FLMRobert/OpenLedModule/Lamp25CMLED/Images/25CMLED__small.jpg

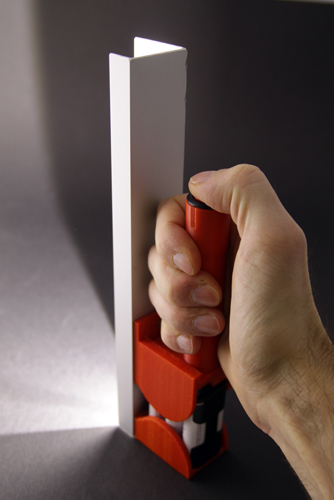
Lamp25CMLED/Images/25CMLED__small.jpg
