FLMRobert/OpenLedModule/Lamp25CMLED/Images/25CMLEDModule1Prototype.JPG

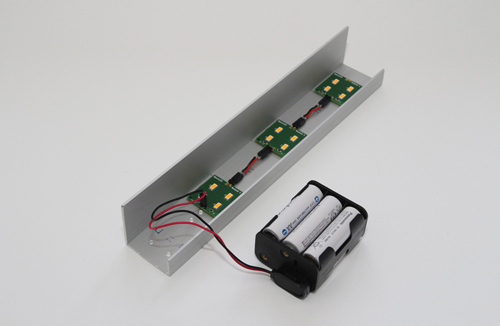
Lamp25CMLED/Images/25CMLEDModule1Prototype.JPG
