FLMRobert/OpenLedModule/Lamp40FLATLED/Images/40FLATLEDPrototype_small.jpg

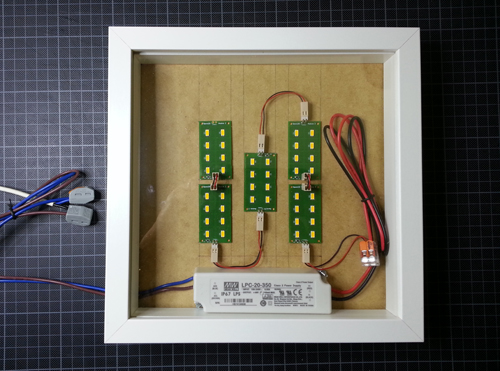
Lamp40FLATLED/Images/40FLATLEDPrototype_small.jpg
