FLMRobert/OpenLedModule/Module2/Images/LEDModul2Detail_02.png

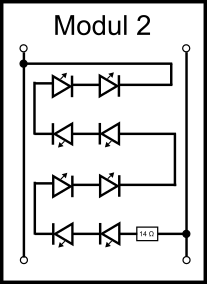
Module2/Images/LEDModul2Detail_02.png
