FLMRobert/OpenLedModule/Lamp25CMLED/Images/Assembly/01.jpg

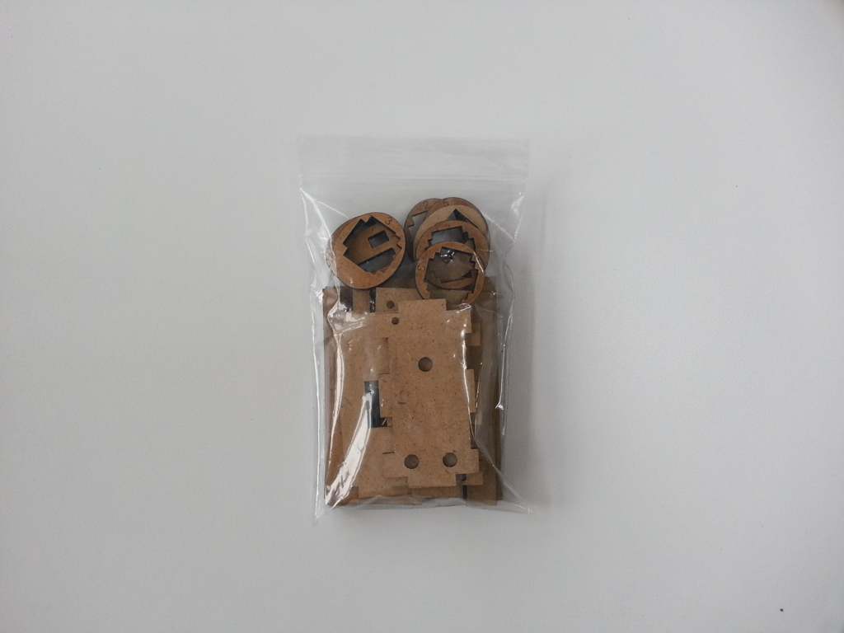
Lamp25CMLED/Images/Assembly/01.jpg
