FLMRobert/OpenLedModule/Lamp25CMLED/Images/Assembly/02.jpg

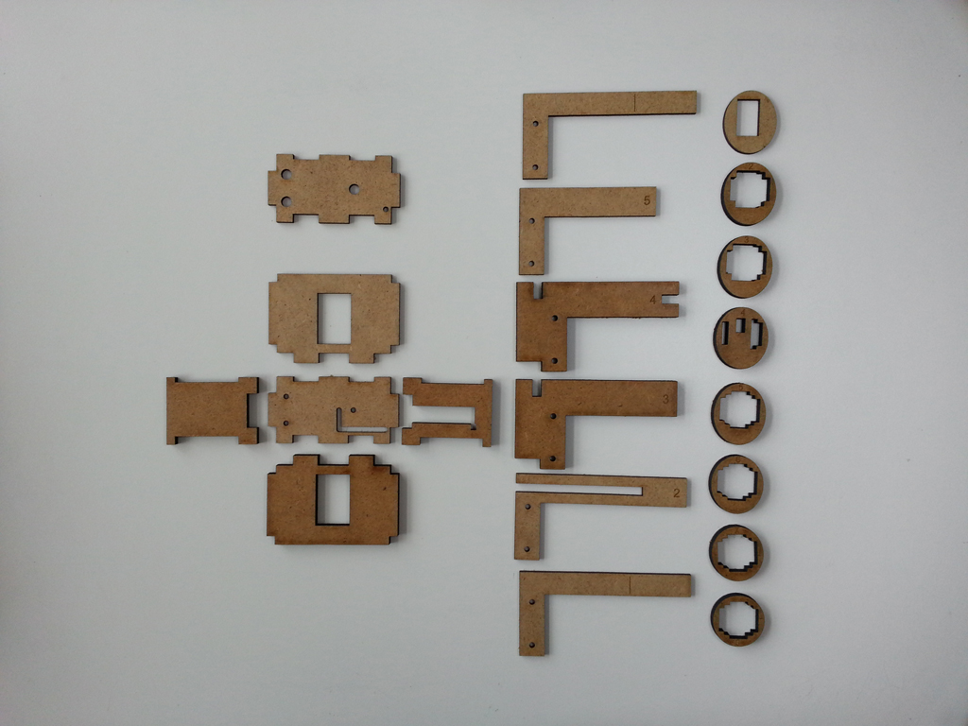
Lamp25CMLED/Images/Assembly/02.jpg
