FLMRobert/OpenLedModule/Lamp25CMLED/Images/Assembly/04.jpg

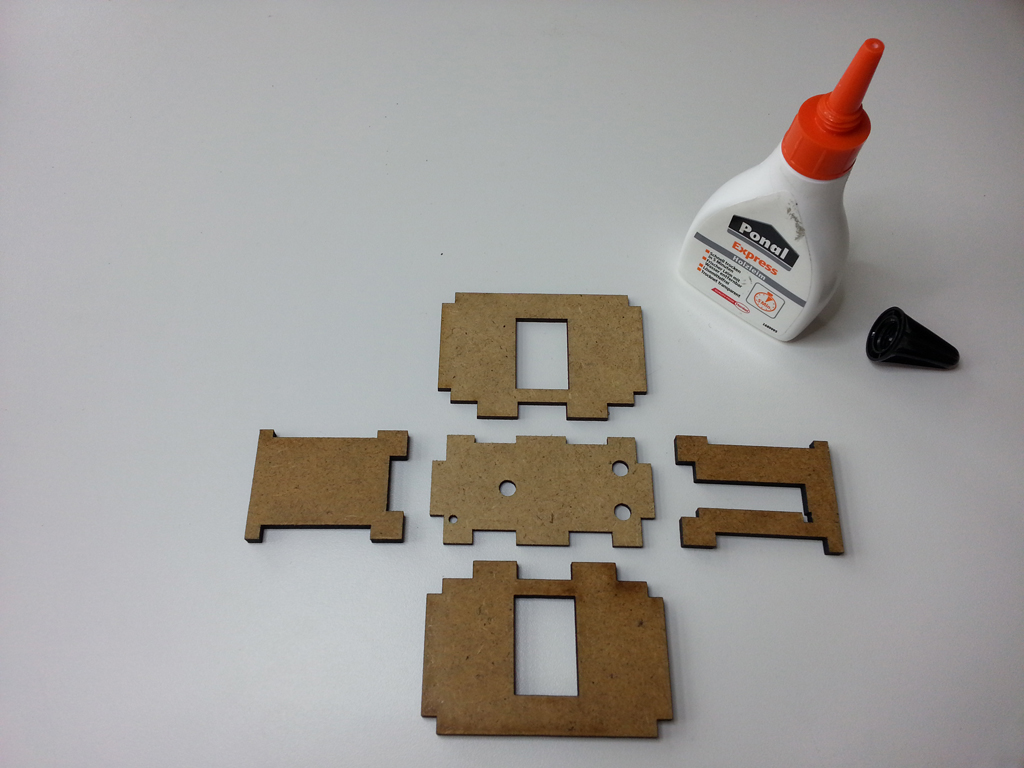
Lamp25CMLED/Images/Assembly/04.jpg
