FLMRobert/OpenLedModule/Lamp25CMLED/Images/Assembly/05.jpg

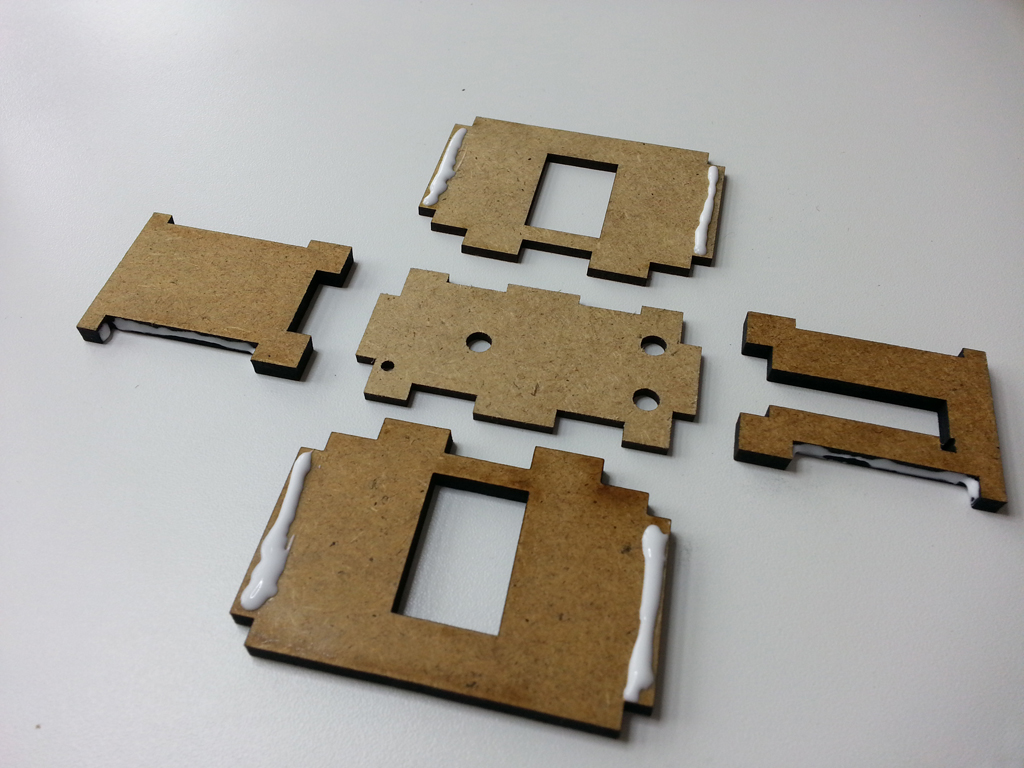
Lamp25CMLED/Images/Assembly/05.jpg
