FLMRobert/OpenLedModule/Lamp25CMLED/Images/Assembly/06.jpg

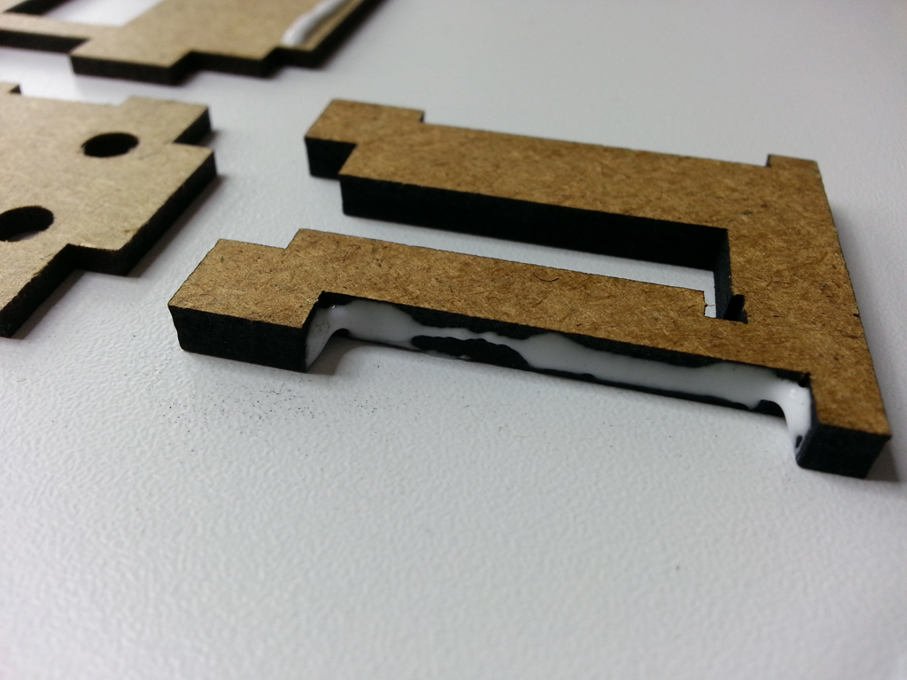
Lamp25CMLED/Images/Assembly/06.jpg
