FLMRobert/OpenLedModule/Lamp25CMLED/Images/Assembly/07.jpg

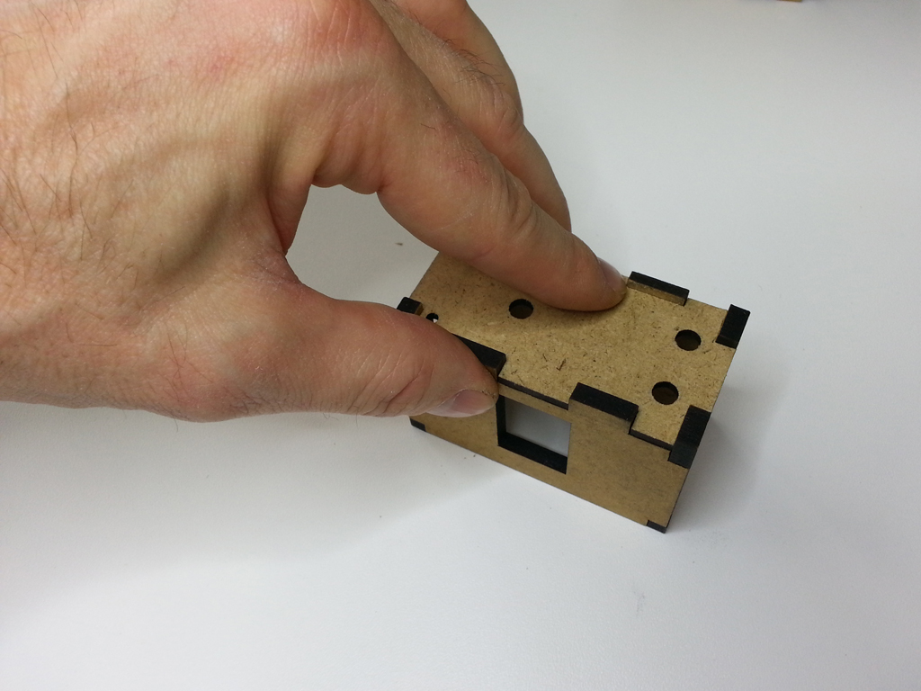
Lamp25CMLED/Images/Assembly/07.jpg
