FLMRobert/OpenLedModule/Lamp25CMLED/Images/Assembly/08.jpg

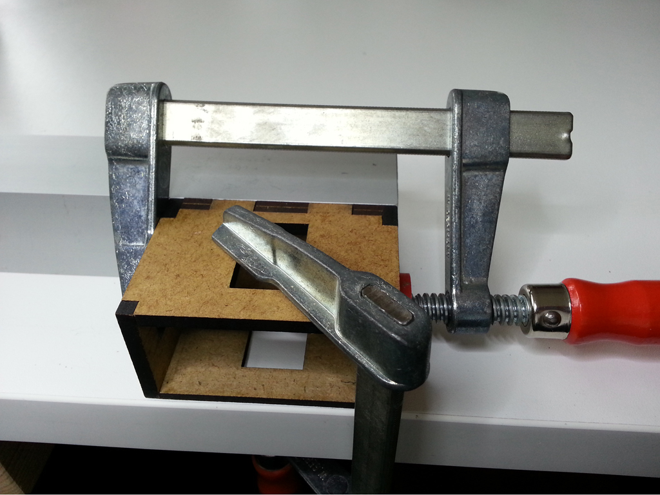
Lamp25CMLED/Images/Assembly/08.jpg
