FLMRobert/OpenLedModule/Lamp25CMLED/Images/Assembly/09.jpg

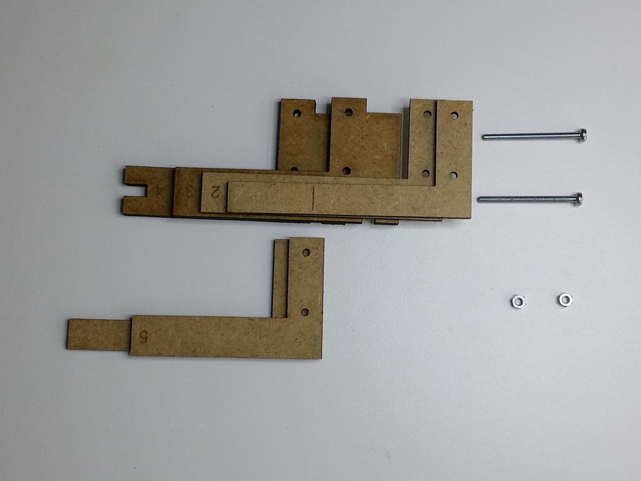
Lamp25CMLED/Images/Assembly/09.jpg
