FLMRobert/OpenLedModule/Lamp25CMLED/Images/Assembly/10.jpg

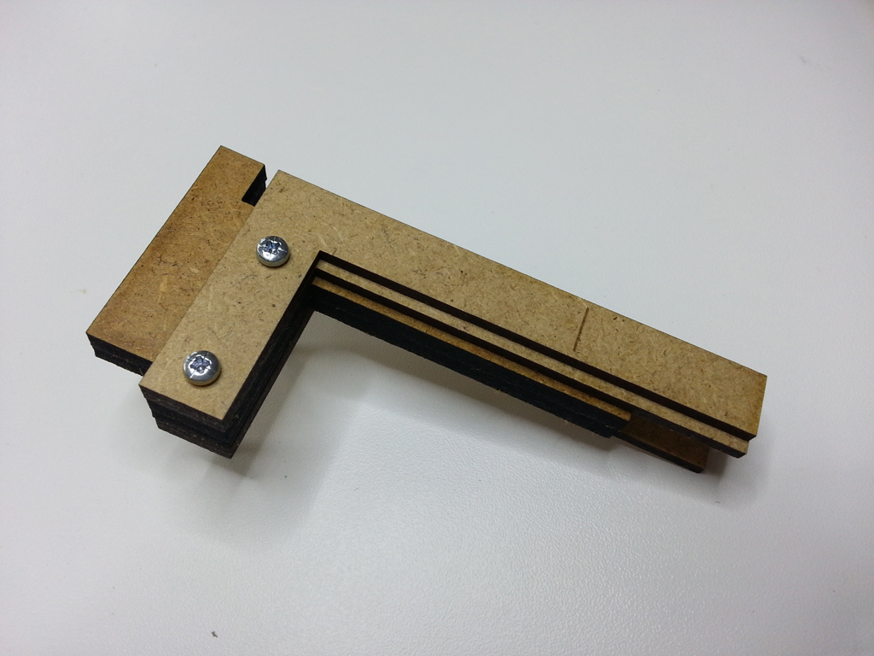
Lamp25CMLED/Images/Assembly/10.jpg
