FLMRobert/OpenLedModule/Lamp25CMLED/Images/Assembly/12.jpg

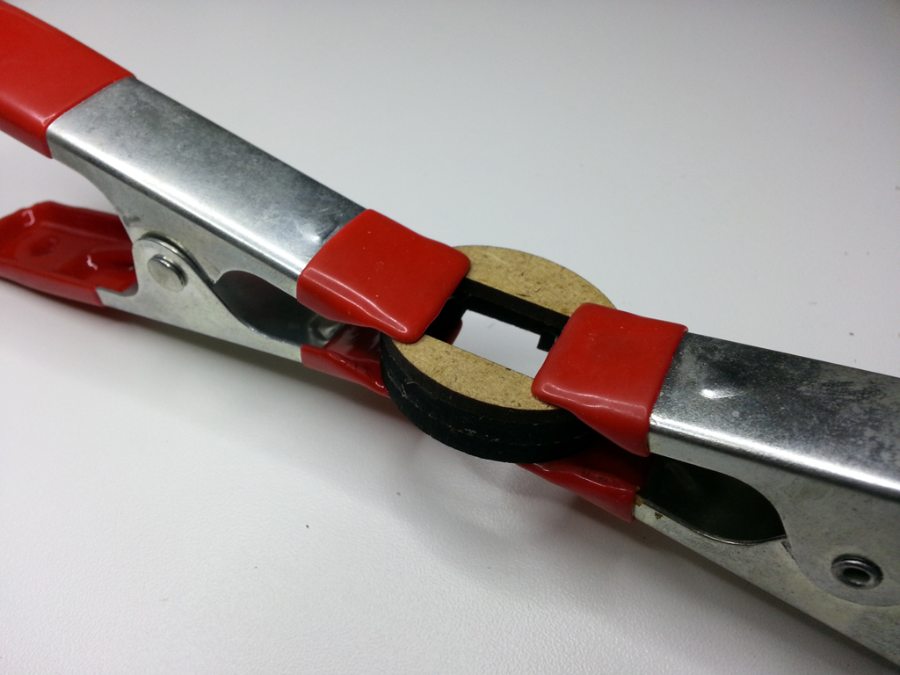
Lamp25CMLED/Images/Assembly/12.jpg
