FLMRobert/OpenLedModule/Lamp25CMLED/Images/Assembly/13.jpg

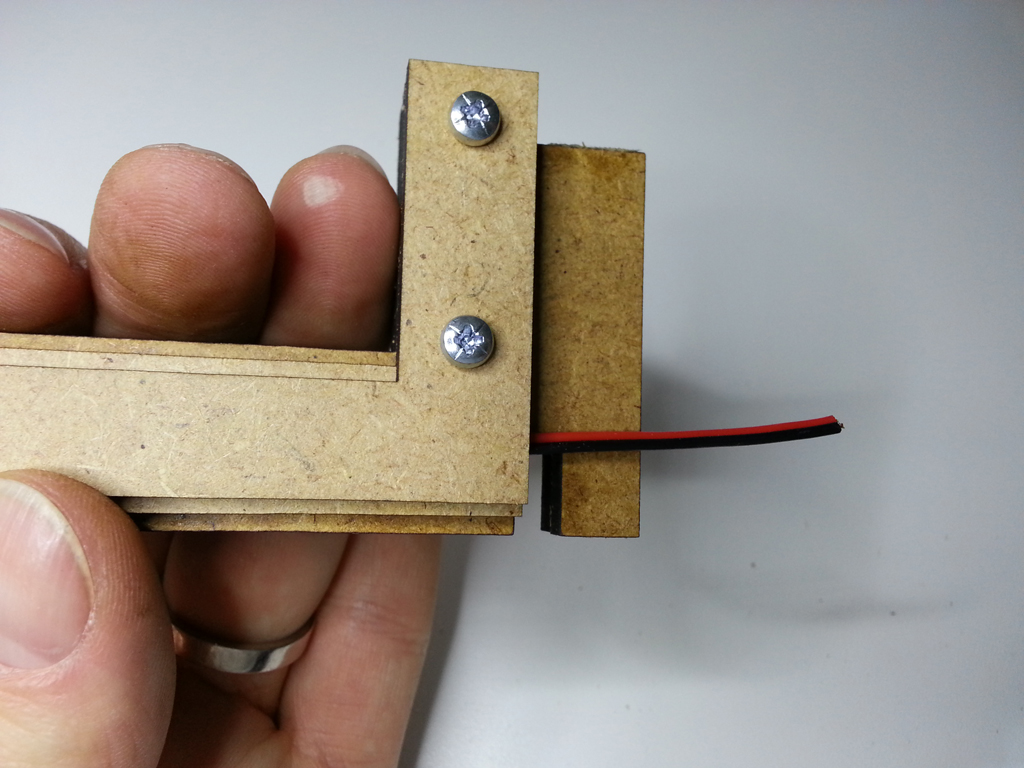
Lamp25CMLED/Images/Assembly/13.jpg
