FLMRobert/OpenLedModule/Lamp25CMLED/Images/Assembly/14.jpg

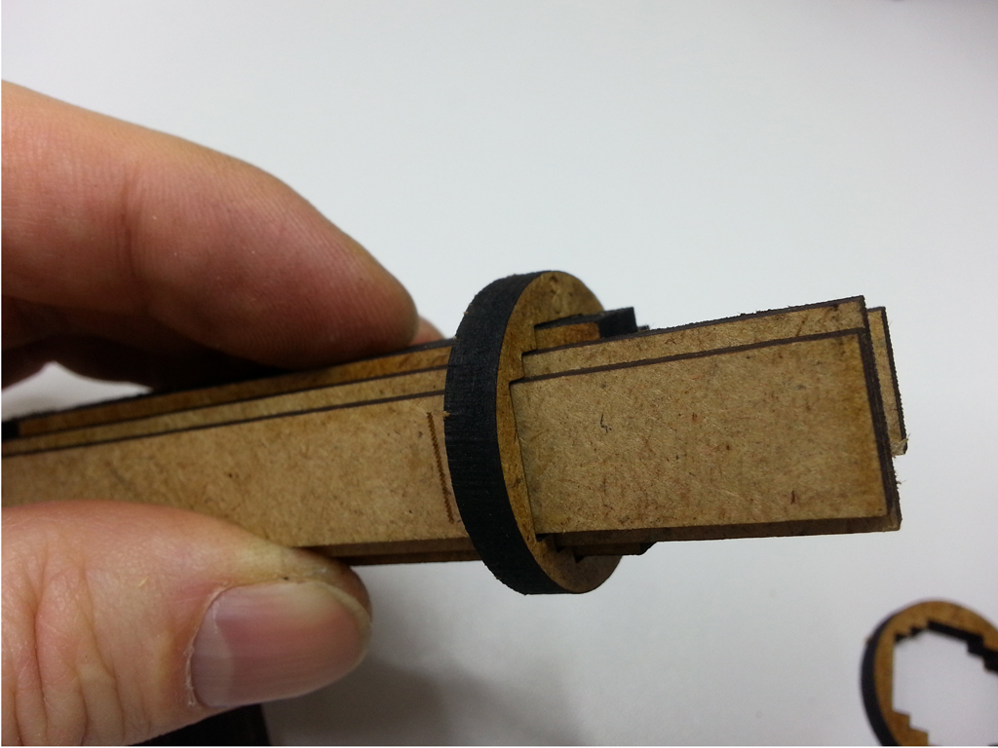
Lamp25CMLED/Images/Assembly/14.jpg
