FLMRobert/OpenLedModule/Lamp25CMLED/Images/Assembly/15.jpg

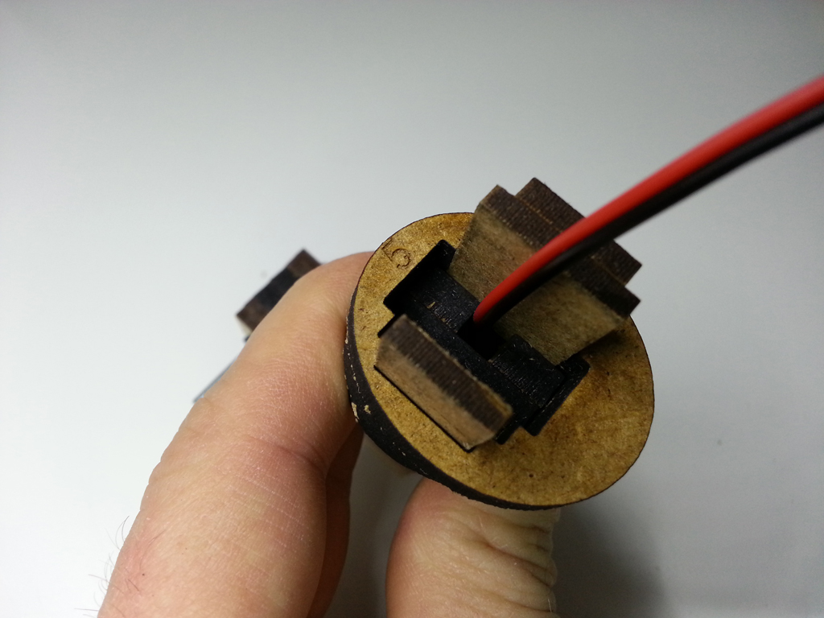
Lamp25CMLED/Images/Assembly/15.jpg
