FLMRobert/OpenLedModule/Lamp25CMLED/Images/Assembly/16.jpg

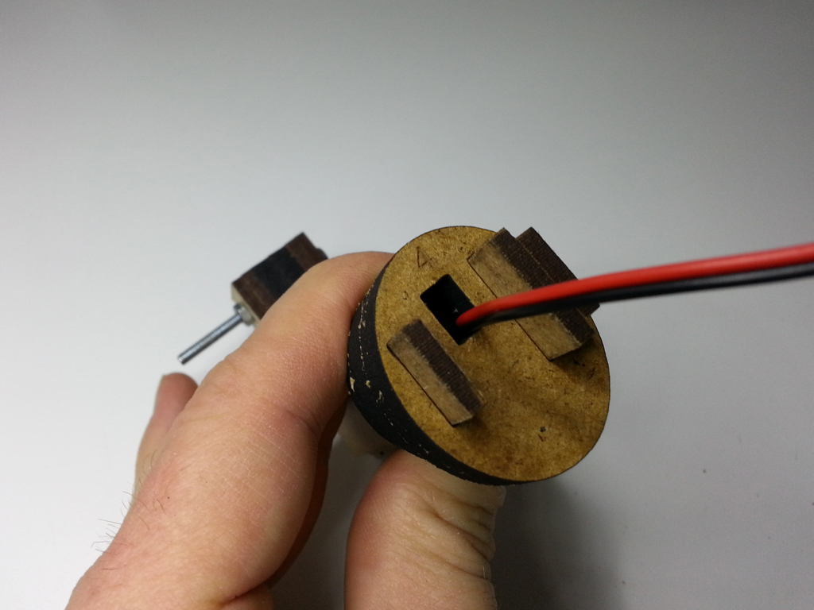
Lamp25CMLED/Images/Assembly/16.jpg
