FLMRobert/OpenLedModule/Lamp25CMLED/Images/Assembly/17.jpg

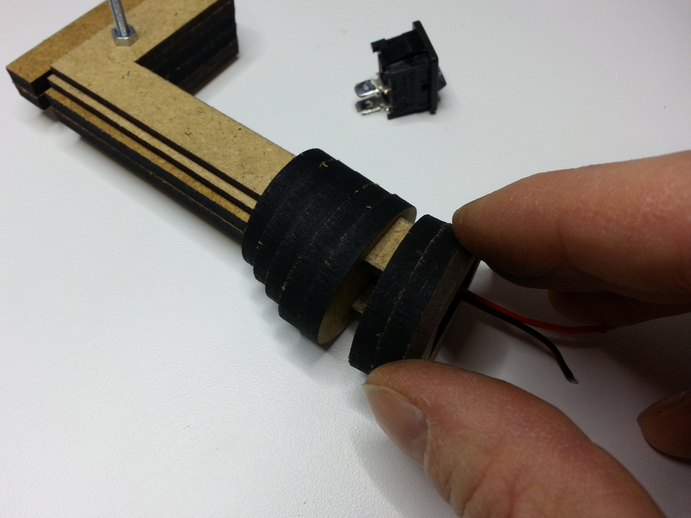
Lamp25CMLED/Images/Assembly/17.jpg
