FLMRobert/OpenLedModule/Lamp25CMLED/Images/Assembly/18.jpg

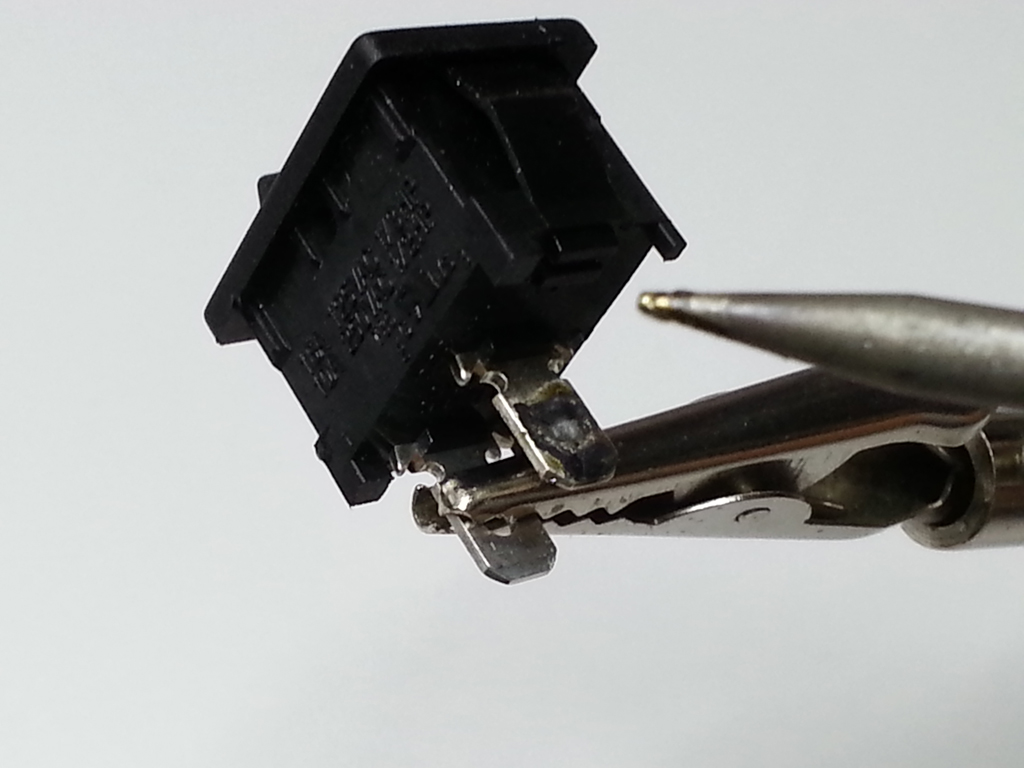
Lamp25CMLED/Images/Assembly/18.jpg
