FLMRobert/OpenLedModule/Lamp25CMLED/Images/Assembly/21.jpg

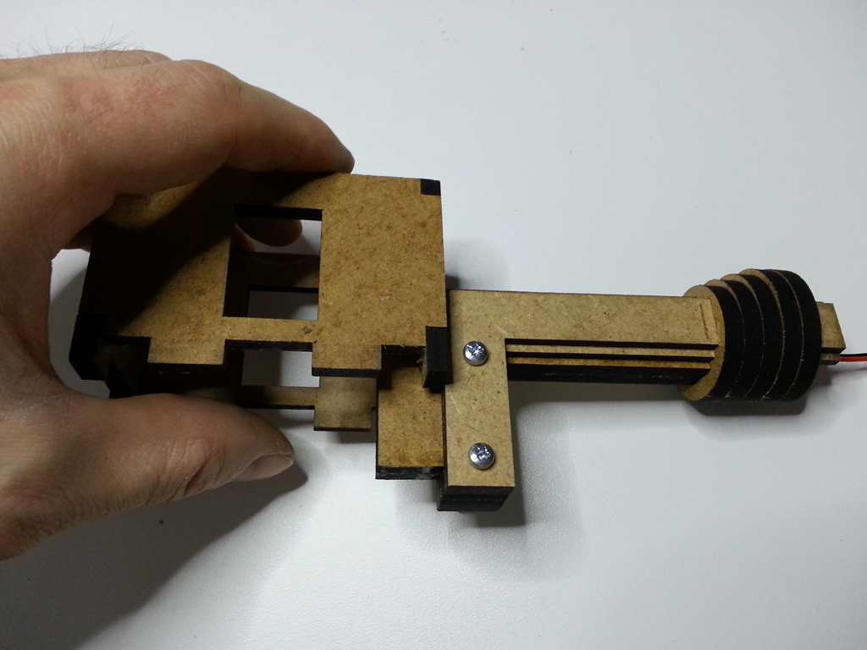
Lamp25CMLED/Images/Assembly/21.jpg
