FLMRobert/OpenLedModule/Lamp25CMLED/Images/Assembly/22.jpg

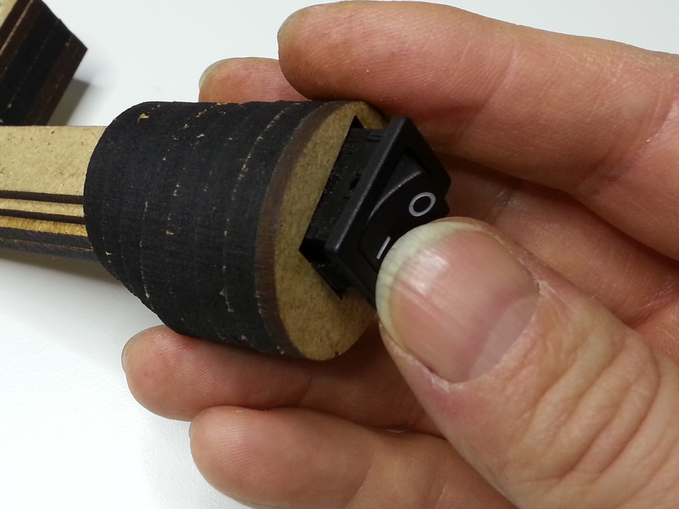
Lamp25CMLED/Images/Assembly/22.jpg
