FLMRobert/OpenLedModule/Lamp25CMLED/Images/Assembly/23.jpg

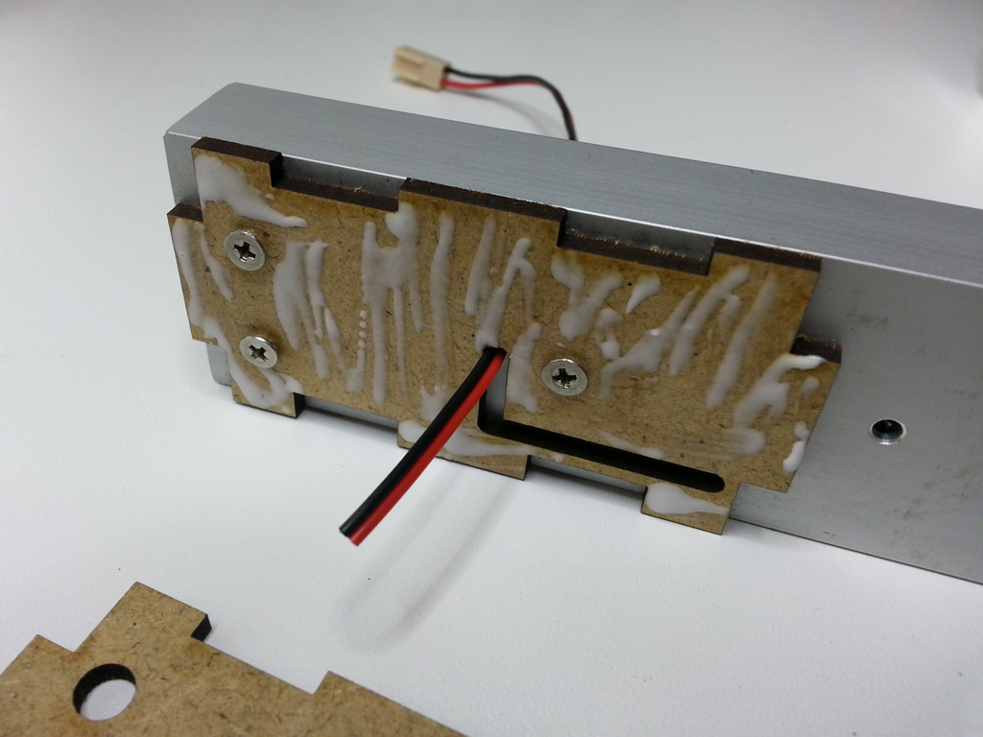
Lamp25CMLED/Images/Assembly/23.jpg
