FLMRobert/OpenLedModule/Lamp25CMLED/Images/Assembly/24.jpg

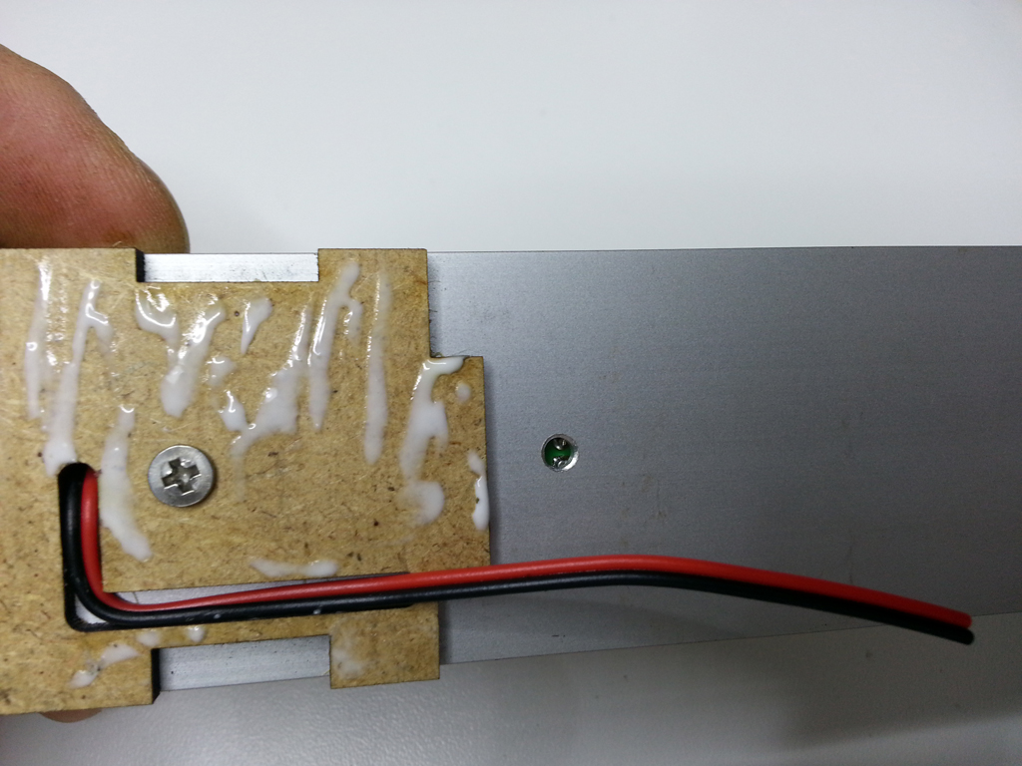
Lamp25CMLED/Images/Assembly/24.jpg
