FLMRobert/OpenLedModule/Lamp25CMLED/Images/Assembly/25.jpg

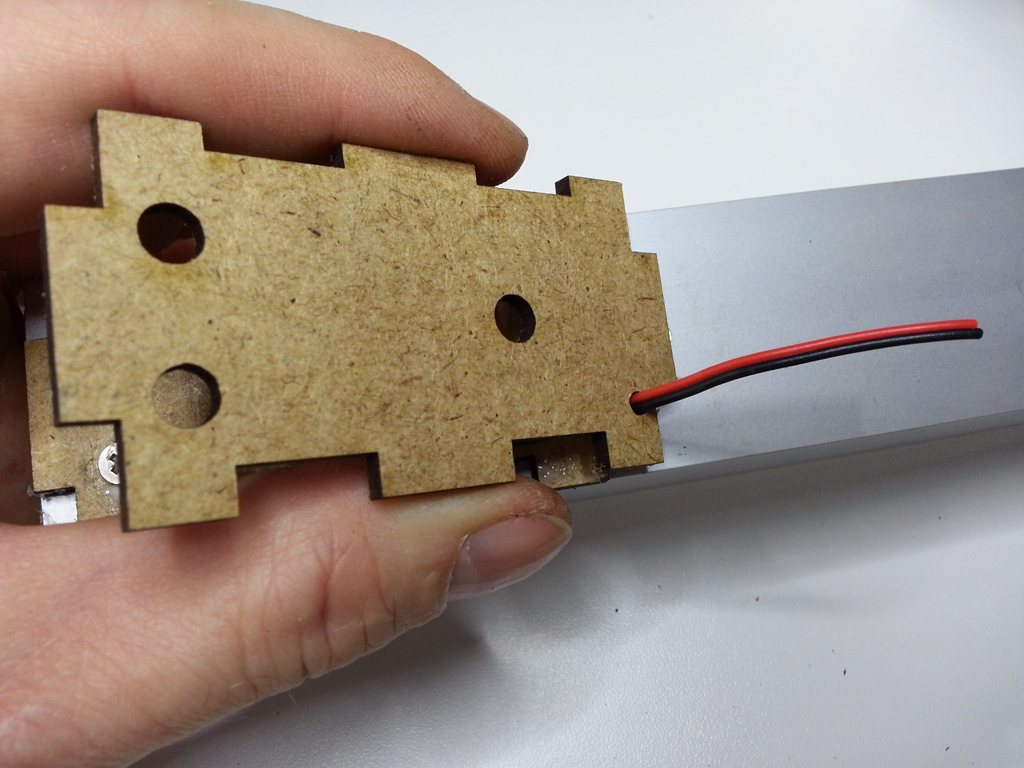
Lamp25CMLED/Images/Assembly/25.jpg
