FLMRobert/OpenLedModule/Lamp25CMLED/Images/Assembly/26.jpg

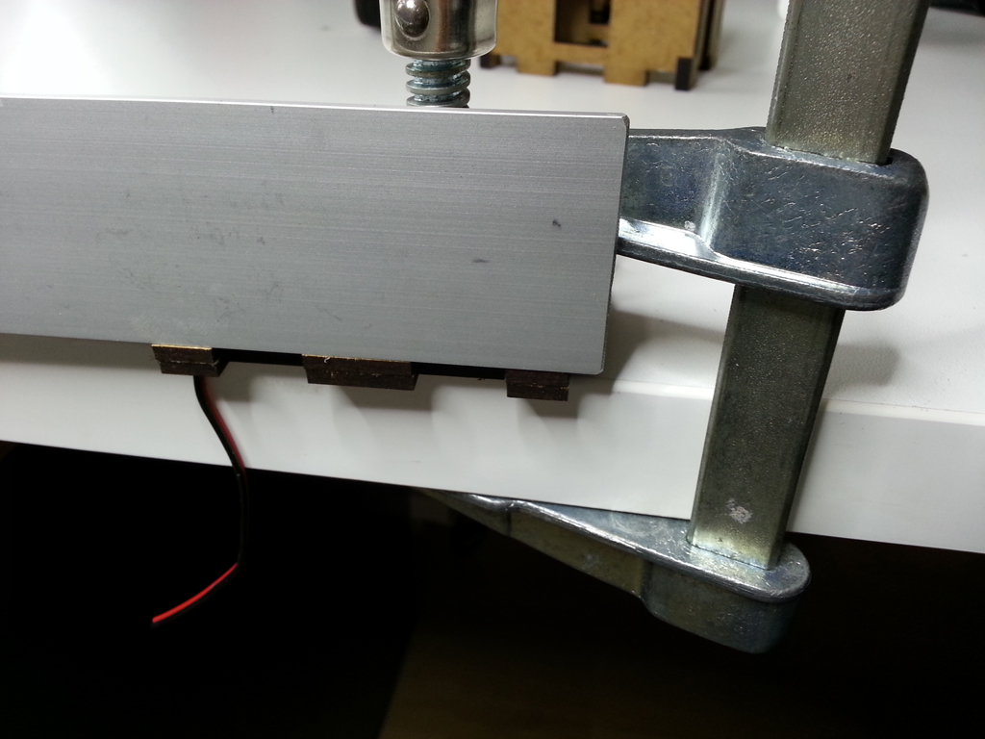
Lamp25CMLED/Images/Assembly/26.jpg
