FLMRobert/OpenLedModule/Lamp25CMLED/Images/Assembly/27.jpg

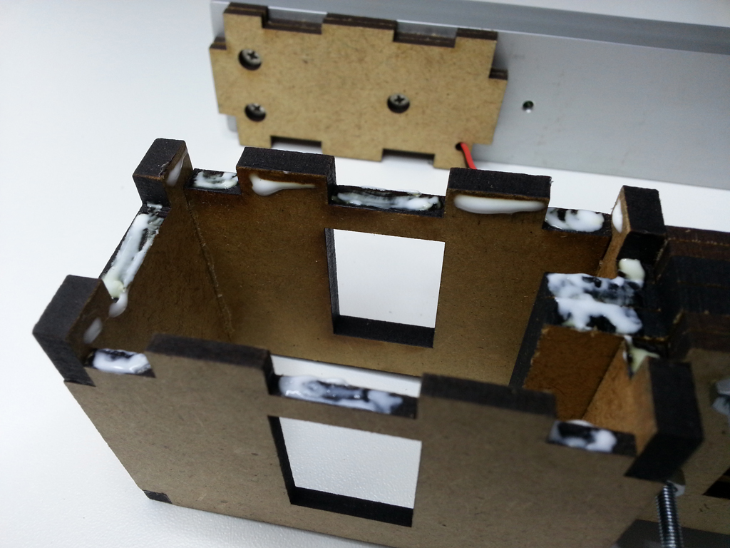
Lamp25CMLED/Images/Assembly/27.jpg
