FLMRobert/OpenLedModule/Lamp25CMLED/Images/Assembly/28.jpg

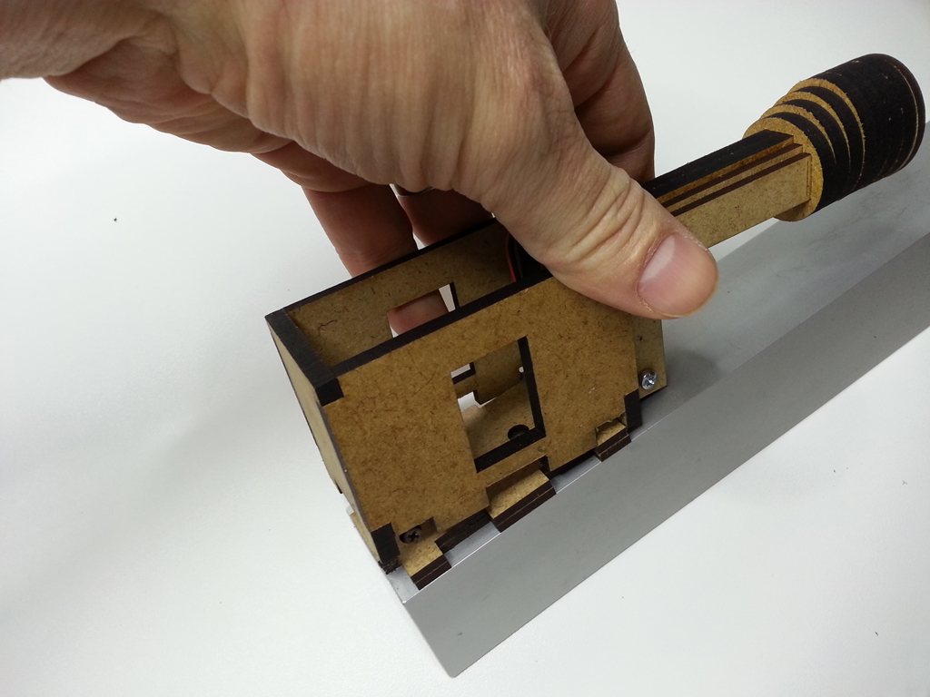
Lamp25CMLED/Images/Assembly/28.jpg
