FLMRobert/OpenLedModule/Lamp25CMLED/Images/Assembly/29.jpg

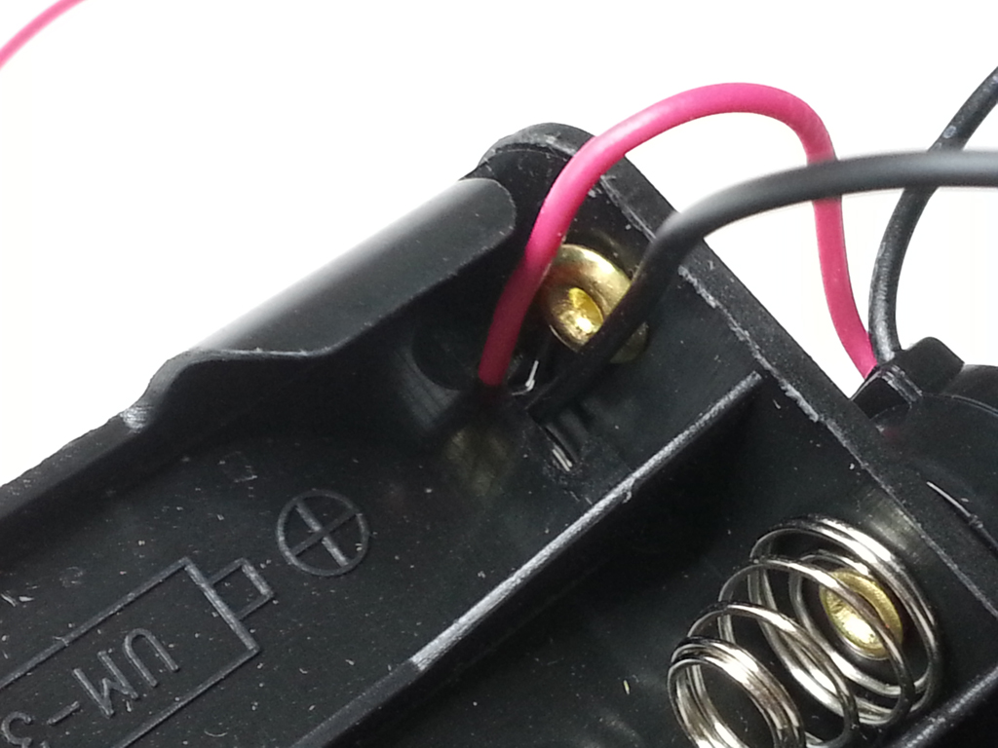
Lamp25CMLED/Images/Assembly/29.jpg
