FLMRobert/OpenLedModule/Lamp25CMLED/Images/Assembly/30.jpg

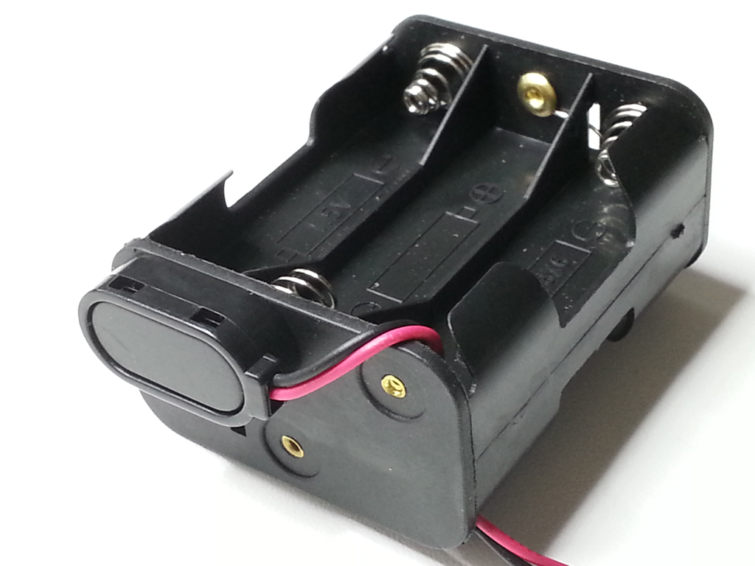
Lamp25CMLED/Images/Assembly/30.jpg
