FLMRobert/OpenLedModule/Lamp25CMLED/Images/Assembly/31.jpg

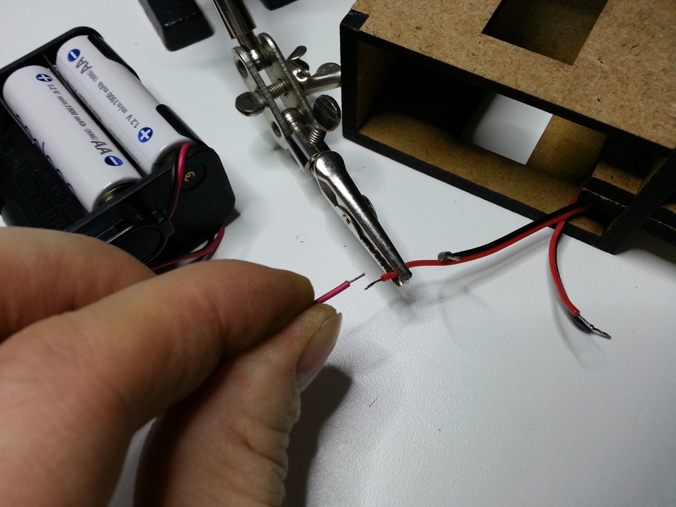
Lamp25CMLED/Images/Assembly/31.jpg
