FLMRobert/OpenLedModule/Lamp25CMLED/Images/Assembly/33.jpg

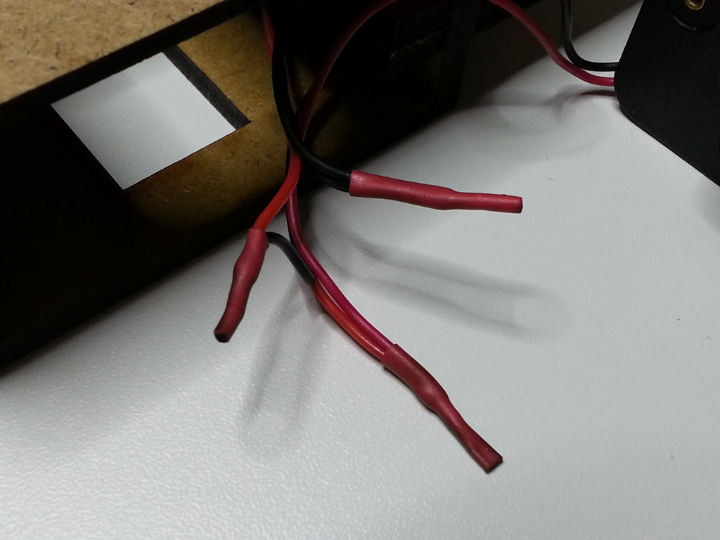
Lamp25CMLED/Images/Assembly/33.jpg
