FLMRobert/OpenLedModule/Lamp25CMLED/Images/Assembly/34.jpg

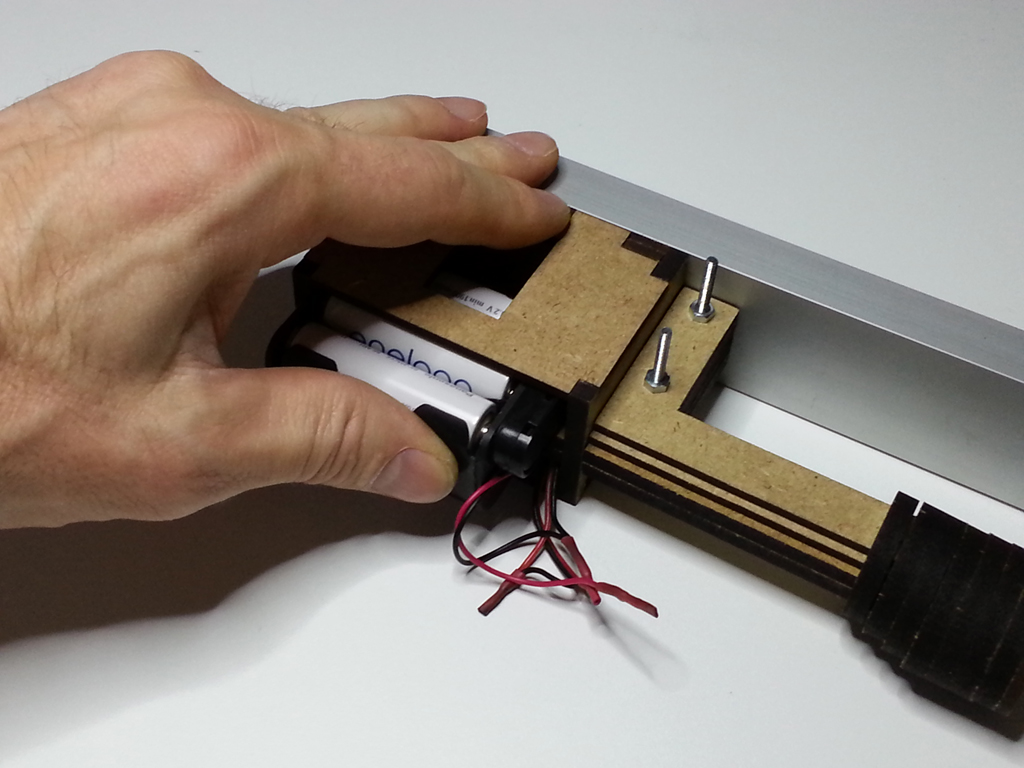
Lamp25CMLED/Images/Assembly/34.jpg
