FLMRobert/OpenLedModule/Lamp25CMLED/Images/Assembly/35.jpg

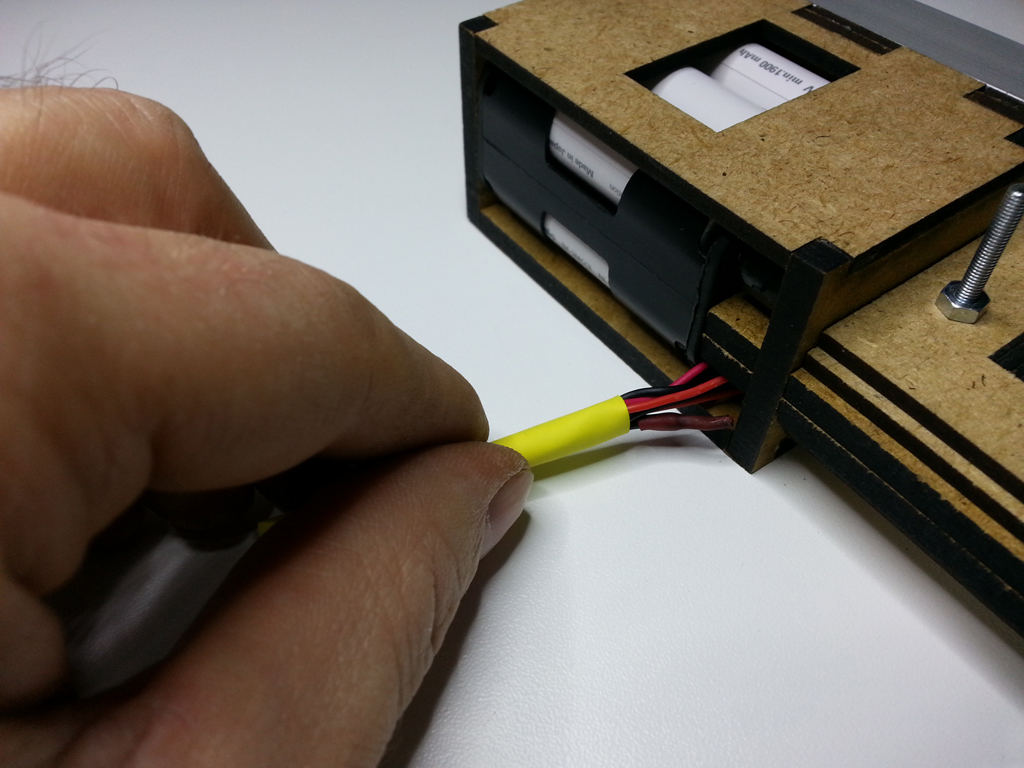
Lamp25CMLED/Images/Assembly/35.jpg
