FLMRobert/OpenLedModule/Lamp25CMLED/Images/Assembly/36.jpg

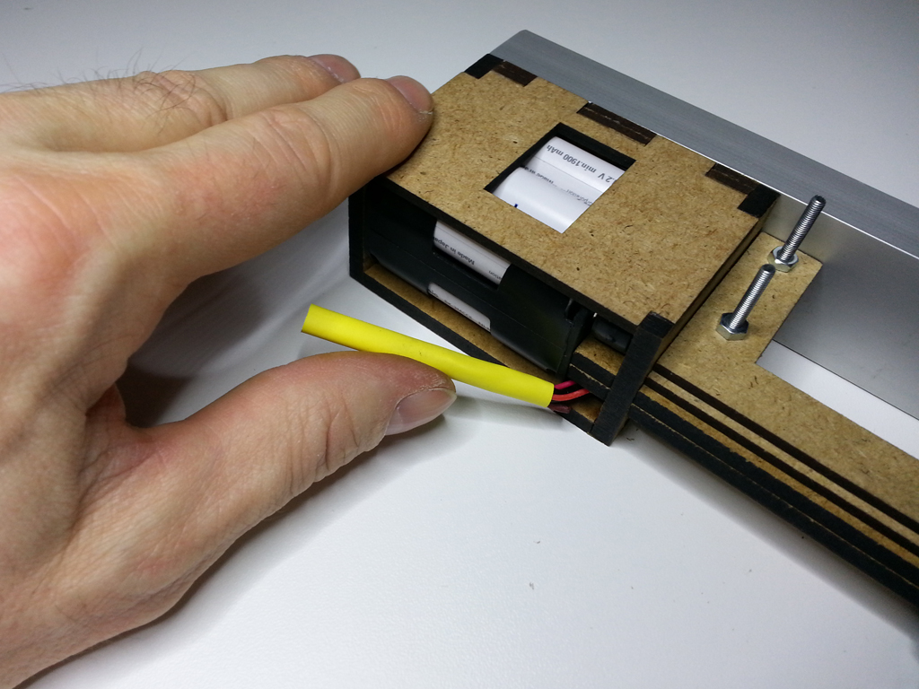
Lamp25CMLED/Images/Assembly/36.jpg
