FLMRobert/OpenLedModule/Module1/Images/Assembly/01.jpg

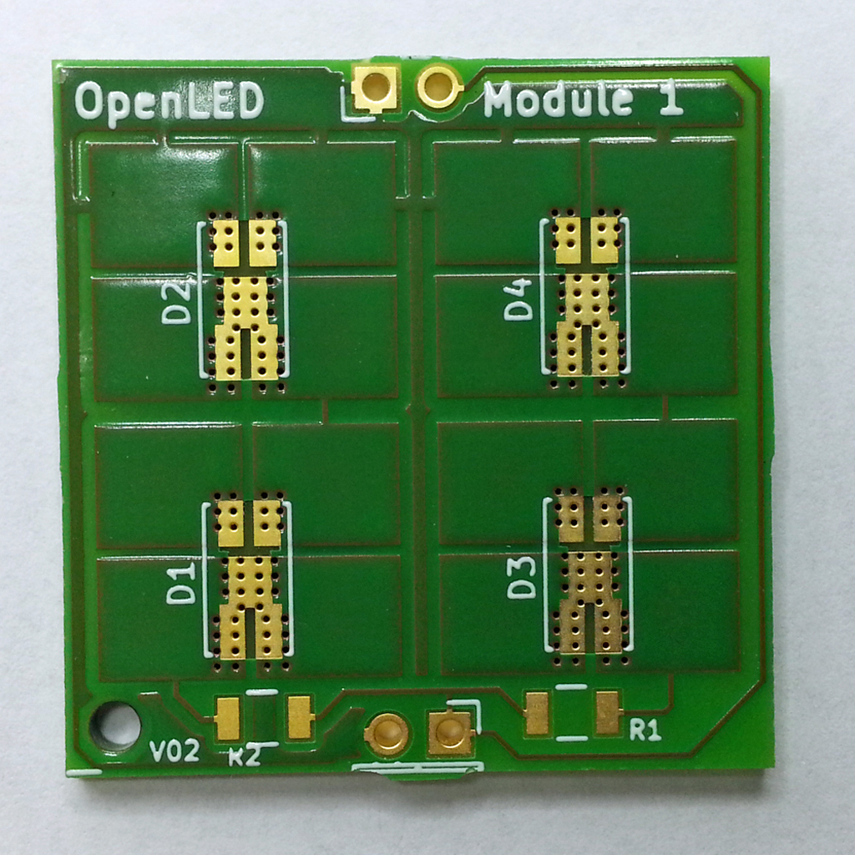
Module1/Images/Assembly/01.jpg
