FLMRobert/OpenLedModule/Module1/Images/Assembly/02.jpg

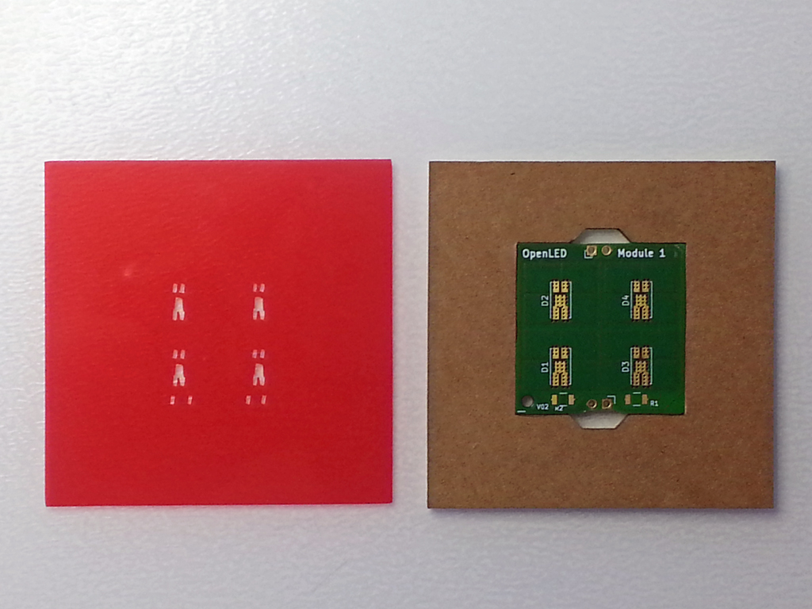
Module1/Images/Assembly/02.jpg
