FLMRobert/OpenLedModule/Module1/Images/Assembly/03a.jpg

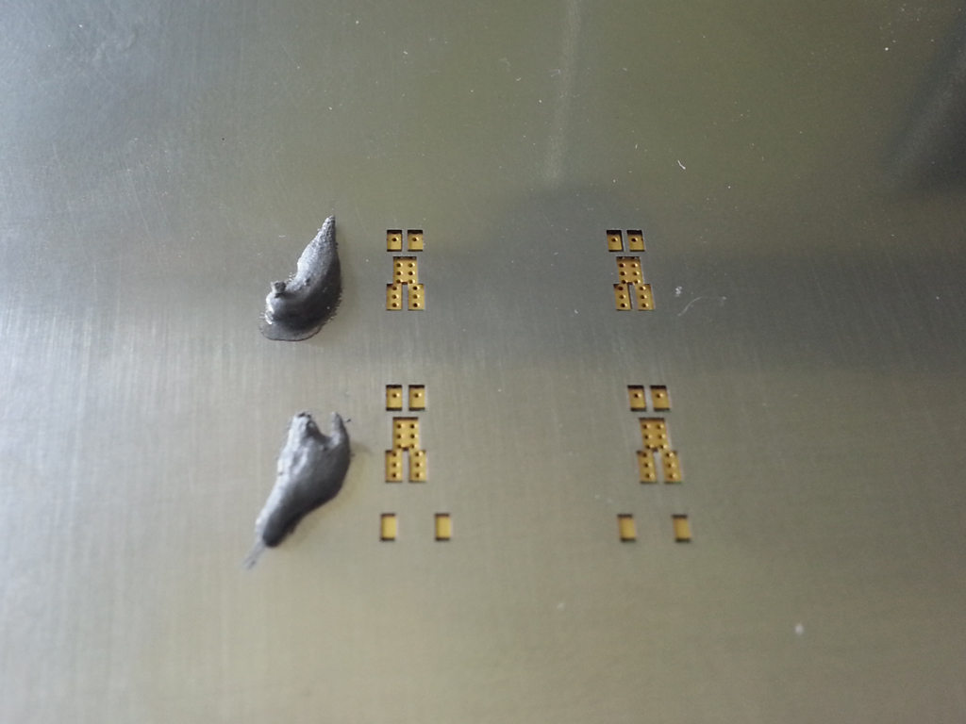
Module1/Images/Assembly/03a.jpg
