FLMRobert/OpenLedModule/Module1/Images/Assembly/04a.jpg

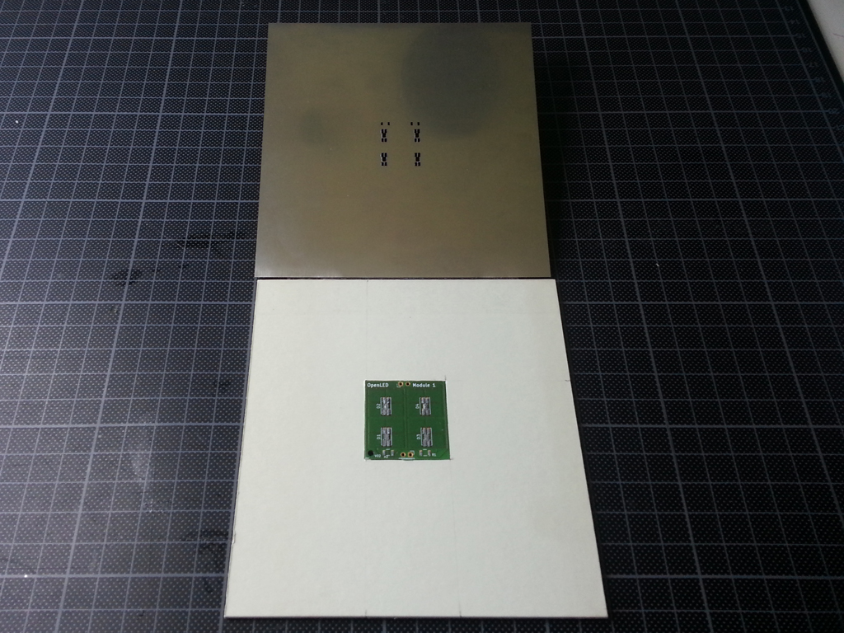
Module1/Images/Assembly/04a.jpg
