FLMRobert/OpenLedModule/Module1/Images/Assembly/04b.jpg

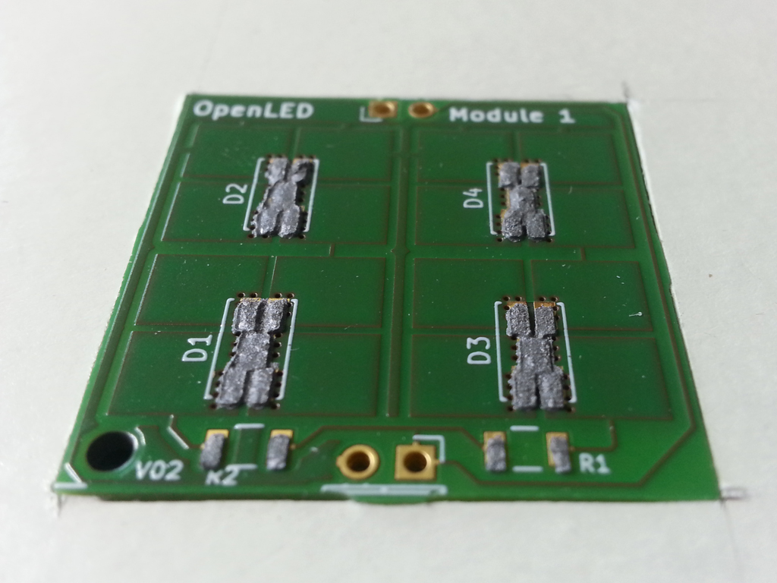
Module1/Images/Assembly/04b.jpg
