FLMRobert/OpenLedModule/Module1/Images/Assembly/05.jpg

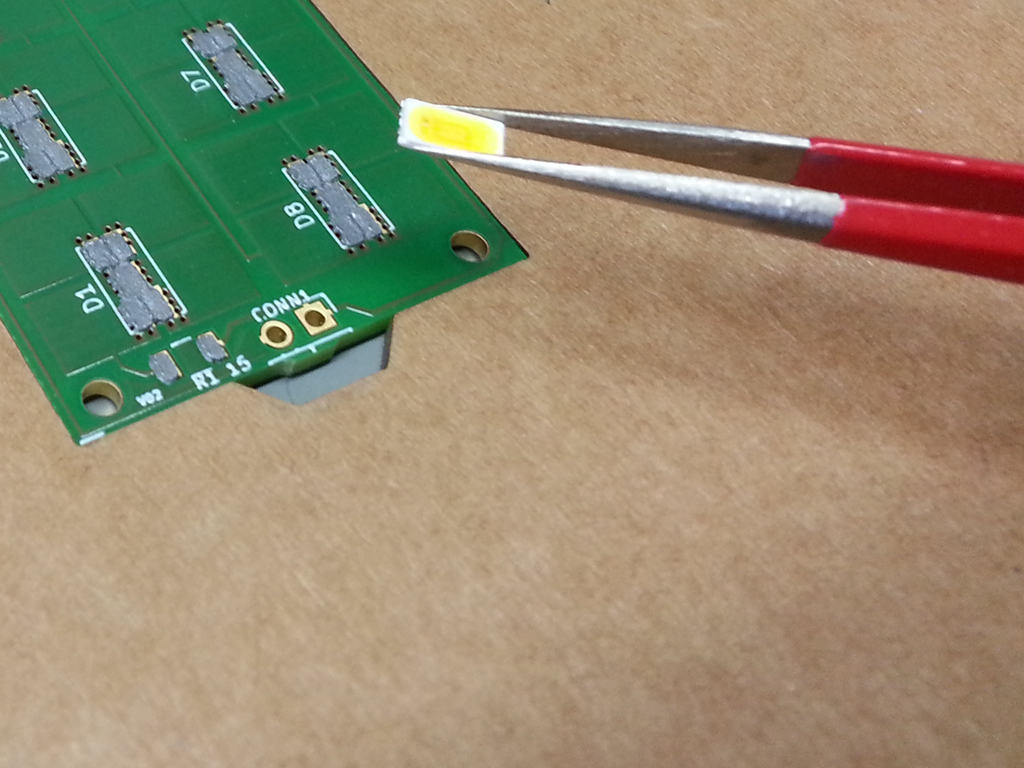
Module1/Images/Assembly/05.jpg
