FLMRobert/OpenLedModule/Module1/Images/Assembly/06.jpg

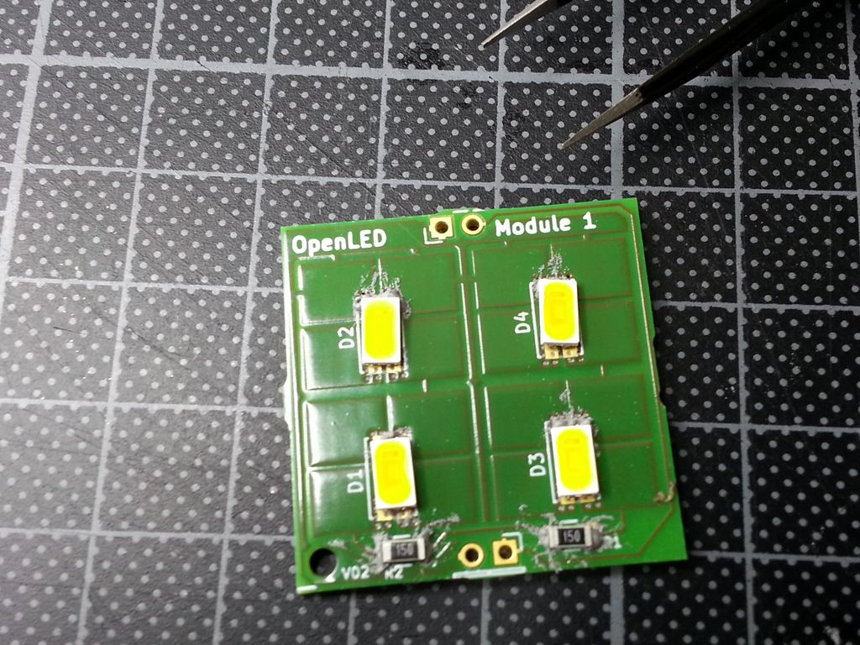
Module1/Images/Assembly/06.jpg
