FLMRobert/OpenLedModule/Module1/Images/Assembly/08.jpg

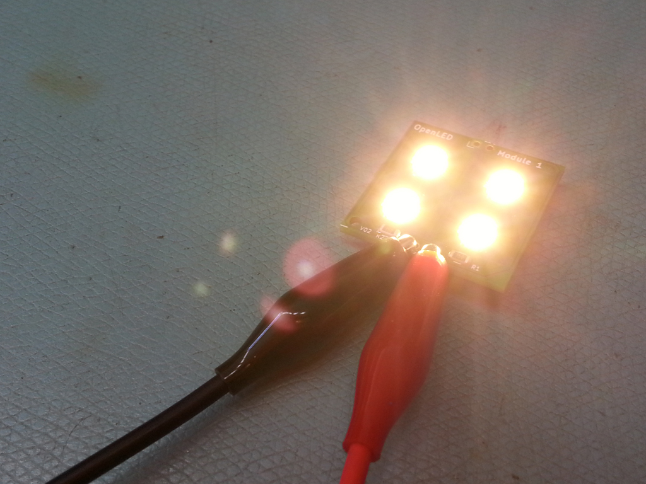
Module1/Images/Assembly/08.jpg
