FLMRobert/OpenLedModule/Module1/Images/Assembly/09.jpg

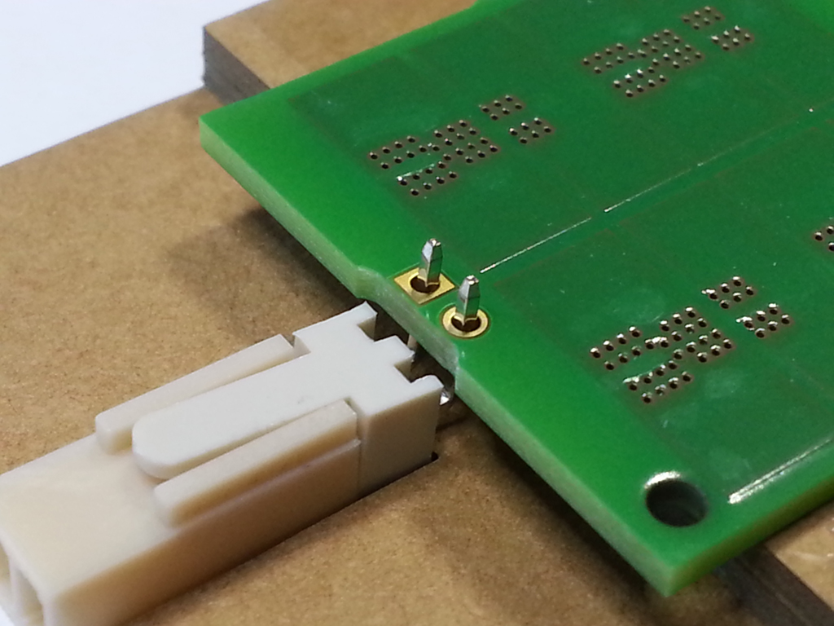
Module1/Images/Assembly/09.jpg
