FLMRobert/OpenLedModule/Lamp40FLATLED/Images/Logbook/40FLATLEDTemperatureExperiment.png

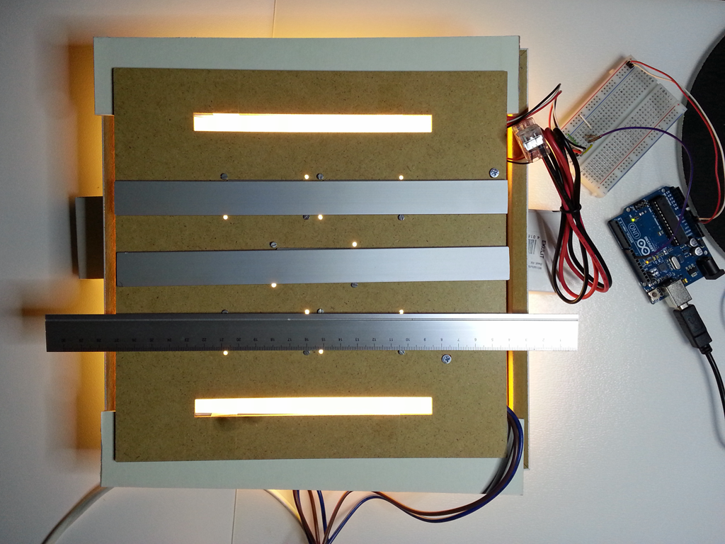
Lamp40FLATLED/Images/Logbook/40FLATLEDTemperatureExperiment.png
