FLMRobert/OpenLedModule/Lamp1MLED/Images/Logbook/1MLEDModules.png

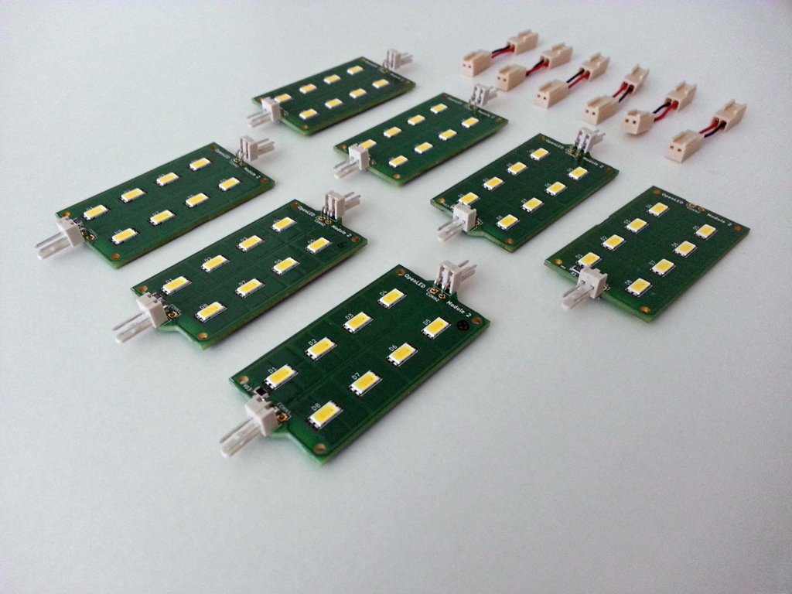
Lamp1MLED/Images/Logbook/1MLEDModules.png
