FLMRobert/OpenLedModule/Lamp1MLED/Images/Logbook/1MLEDNormalTape.png

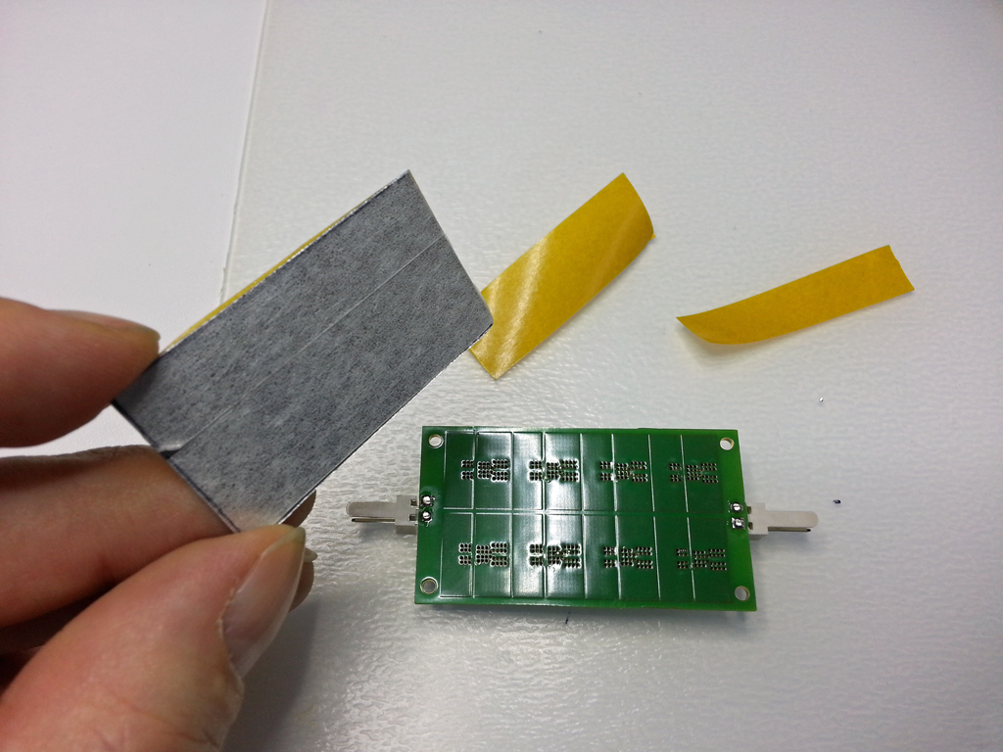
Lamp1MLED/Images/Logbook/1MLEDNormalTape.png
