FLMRobert/OpenLedModule/Lamp1MLED/Images/Logbook/1MLEDThermalTape.png

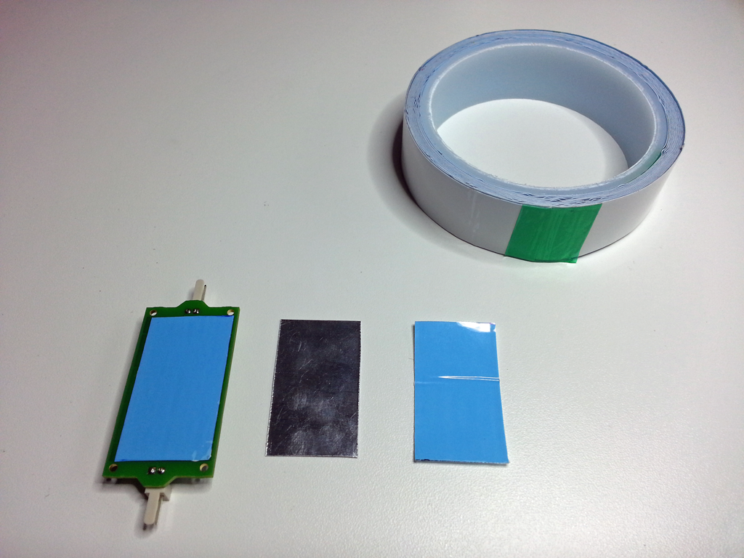
Lamp1MLED/Images/Logbook/1MLEDThermalTape.png
