FLMRobert/OpenLedModule/Lamp25CMLED/Images/Logbook/25CMLEDCardboard.png

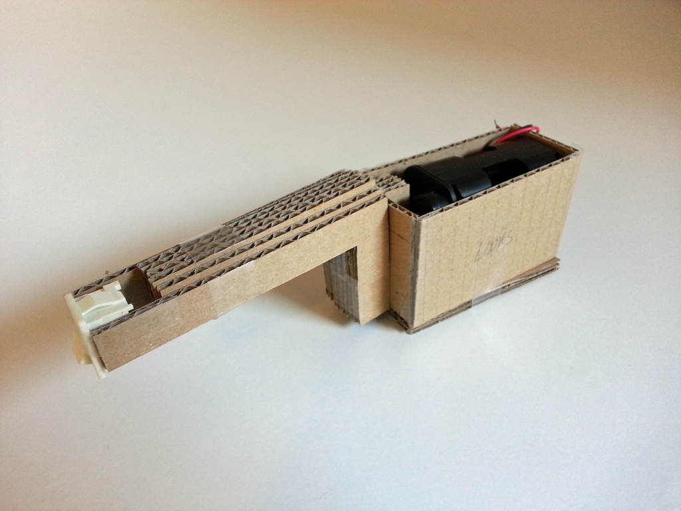
Lamp25CMLED/Images/Logbook/25CMLEDCardboard.png
