FLMRobert/OpenLedModule/Lamp25CMLED/Images/Logbook/25CMLEDCardboardBattery.png

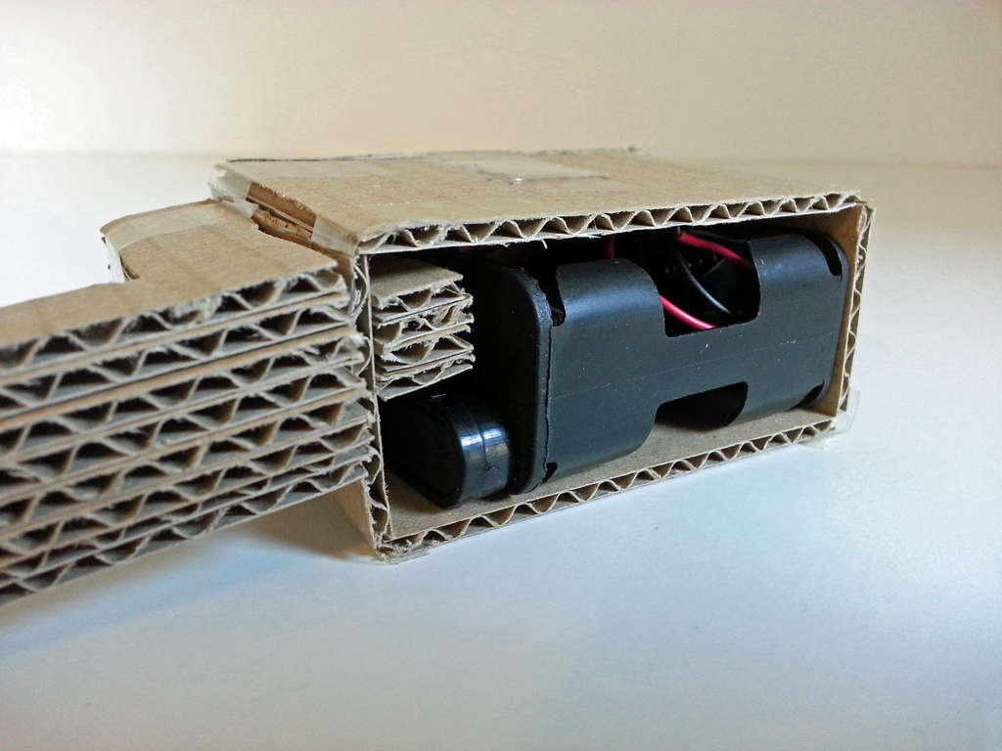
Lamp25CMLED/Images/Logbook/25CMLEDCardboardBattery.png
