FLMRobert/OpenLedModule/Lamp25CMLED/Images/Logbook/25CMLEDCardboardSwitch.png

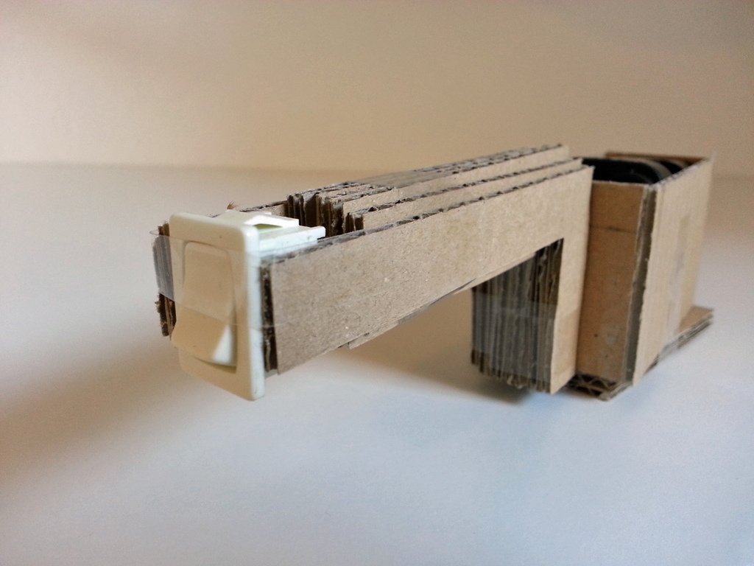
Lamp25CMLED/Images/Logbook/25CMLEDCardboardSwitch.png
