FLMRobert/OpenLedModule/Lamp25CMLED/Images/Logbook/25CMLEDLasercut.png

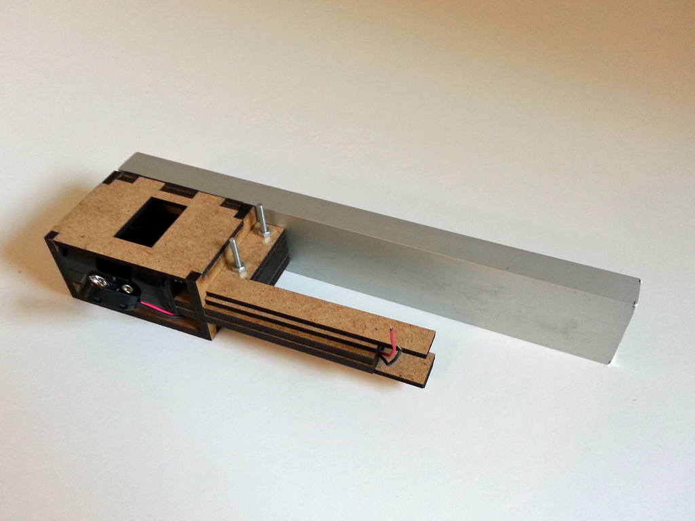
Lamp25CMLED/Images/Logbook/25CMLEDLasercut.png
