FLMRobert/OpenLedModule/Lamp25CMLED/Images/Logbook/25CMLEDLasercutDetailCable.png

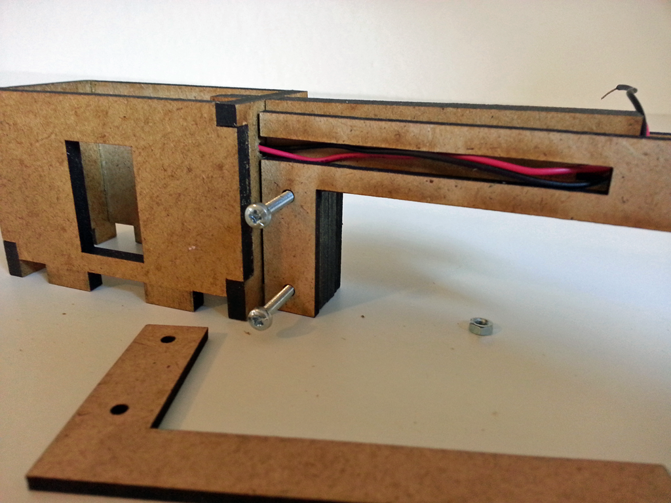
Lamp25CMLED/Images/Logbook/25CMLEDLasercutDetailCable.png
