FLMRobert/OpenLedModule/Lamp25CMLED/Images/Logbook/25CMLEDLasercutDetailInner.png

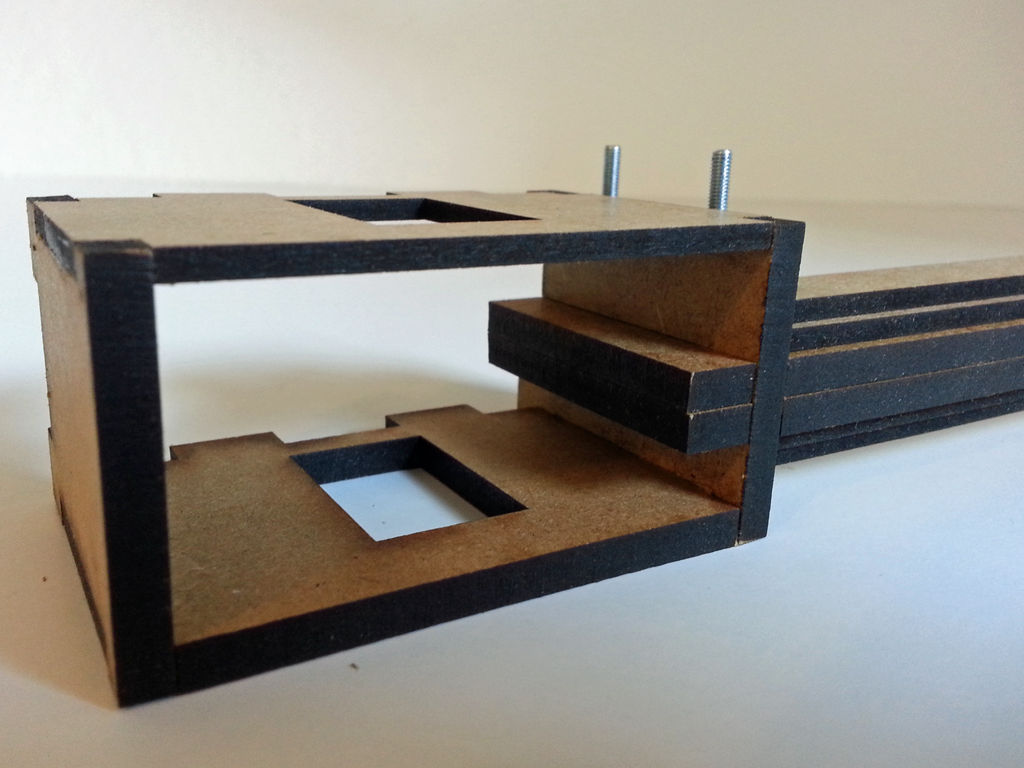
Lamp25CMLED/Images/Logbook/25CMLEDLasercutDetailInner.png
