FLMRobert/OpenLedModule/Lamp25CMLED/Images/Logbook/25CMLEDLasercutDetailMount.png

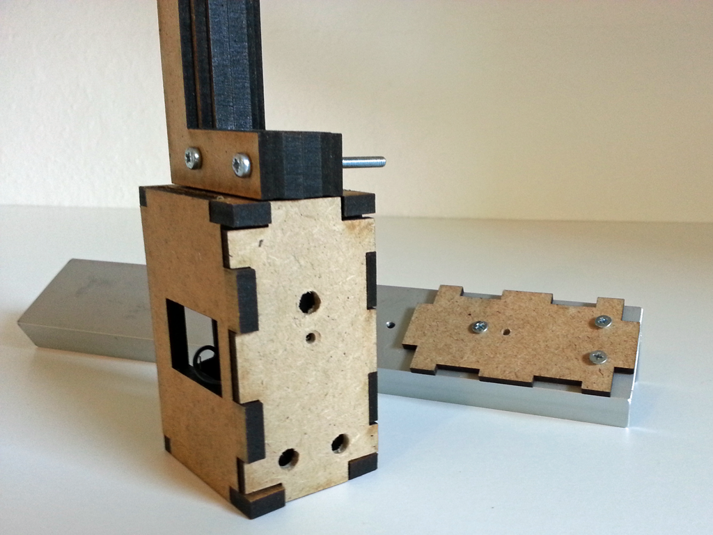
Lamp25CMLED/Images/Logbook/25CMLEDLasercutDetailMount.png
