FLMRobert/OpenLedModule/Lamp40FLATLED/Images/Logbook/40FLATLEDTemperatureCurves.png

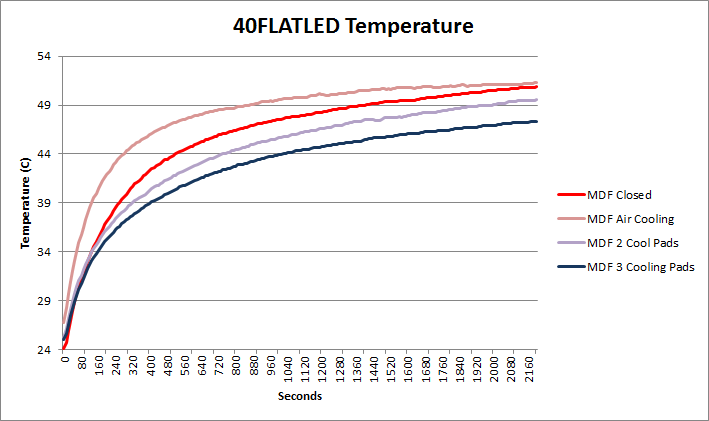
Lamp40FLATLED/Images/Logbook/40FLATLEDTemperatureCurves.png
